bchelf/microNES/src/common/apu_micrones.c

#include "apu_micrones.h"

#include <math.h>
#include <string.h>

enum {
    APU_FRAME_STEP_1 = 3729,
    APU_FRAME_STEP_2 = 7457,
    APU_FRAME_STEP_3 = 11186,
    APU_FRAME_STEP_4 = 14915,
    APU_FRAME_STEP_5 = 18641,
};

static const uint8_t k_apu_length_table[32] = {
    10, 254, 20,  2, 40,  4, 80,  6,
    160, 8, 60, 10, 14, 12, 26, 14,
    12, 16, 24, 18, 48, 20, 96, 22,
    192, 24, 72, 26, 16, 28, 32, 30,
};

static const uint8_t k_apu_pulse_duty[4][8] = {
    { 0, 1, 0, 0, 0, 0, 0, 0 },
    { 0, 1, 1, 0, 0, 0, 0, 0 },
    { 0, 1, 1, 1, 1, 0, 0, 0 },
    { 1, 0, 0, 1, 1, 1, 1, 1 },
};

static const uint8_t k_apu_triangle_sequence[32] = {
    15, 14, 13, 12, 11, 10, 9, 8,
    7,  6,  5,  4,  3,  2,  1, 0,
    0,  1,  2,  3,  4,  5,  6, 7,
    8,  9, 10, 11, 12, 13, 14, 15,
};

static const uint16_t k_apu_noise_period_table[16] = {
    4, 8, 16, 32, 64, 96, 128, 160,
    202, 254, 380, 508, 762, 1016, 2034, 4068,
};

/* NTSC DMC rate table: CPU cycles per output-unit clock.
 * Source: NesDev wiki, APU DMC. PAL uses a different table; we are NTSC-only. */
static const uint16_t k_apu_dmc_rate_table[16] = {
    428, 380, 340, 320, 286, 254, 226, 214,
    190, 160, 142, 128, 106,  84,  72,  54,
};

enum {
    APU_TEST_TONE_PULSE_PHASE = 0,
    APU_TEST_TONE_TRIANGLE_PHASE = 1,
};

static const uint32_t k_apu_test_tone_step_pulse1 =
    (uint32_t)((440ull << 32) / APU_OUTPUT_SAMPLE_RATE);
static const uint32_t k_apu_test_tone_step_triangle =
    (uint32_t)((220ull << 32) / APU_OUTPUT_SAMPLE_RATE);

static void apu_stats_note(ApuDebugSampleStats *stats, int32_t value) {
#if MICRONES_ENABLE_APU_DEBUG_METRICS
    if (stats->sample_count == 0) {
        stats->min_value = value;
        stats->max_value = value;
    } else {
        if (value < stats->min_value) {
            stats->min_value = value;
        }
        if (value > stats->max_value) {
            stats->max_value = value;
        }
    }
    ++stats->sample_count;
    if (value != 0) {
        ++stats->nonzero_sample_count;
    }
    stats->abs_sum += (uint64_t)(value < 0 ? -value : value);
#else
    (void)stats;
    (void)value;
#endif
}

static void apu_pcm_push(Apu *apu, int16_t sample) {
    if (apu->pcm_count >= APU_PCM_CAPACITY) {
        ++apu->dropped_samples;
        return;
    }

    apu->pcm[apu->pcm_write_index] = sample;
    apu->pcm_write_index = (apu->pcm_write_index + 1u) % APU_PCM_CAPACITY;
    ++apu->pcm_count;
    ++apu->sample_count;
}

static void apu_capture_pulse_state(const ApuPulseChannel *src, ApuDebugPulseState *dst) {
    dst->enabled = src->enabled;
    dst->length_halt = src->length_halt;
    dst->constant_volume = src->constant_volume;
    dst->sweep_enabled = src->sweep_enabled;
    dst->duty = src->duty;
    dst->duty_step = src->duty_step;
    dst->volume_period = src->volume_period;
    dst->envelope_decay = src->envelope_decay;
    dst->length_counter = src->length_counter;
    dst->timer_period = src->timer_period;
    dst->timer_counter = src->timer_counter;
}

static void apu_capture_triangle_state(const ApuTriangleChannel *src, ApuDebugTriangleState *dst) {
    dst->enabled = src->enabled;
    dst->control_flag = src->control_flag;
    dst->linear_reload_flag = src->linear_reload_flag;
    dst->sequence_step = src->sequence_step;
    dst->linear_reload_value = src->linear_reload_value;
    dst->linear_counter = src->linear_counter;
    dst->length_counter = src->length_counter;
    dst->timer_period = src->timer_period;
    dst->timer_counter = src->timer_counter;
}

static void apu_capture_noise_state(const ApuNoiseChannel *src, ApuDebugNoiseState *dst) {
    dst->enabled = src->enabled;
    dst->length_halt = src->length_halt;
    dst->constant_volume = src->constant_volume;
    dst->mode = src->mode;
    dst->volume_period = src->volume_period;
    dst->envelope_decay = src->envelope_decay;
    dst->length_counter = src->length_counter;
    dst->period_index = src->period_index;
    dst->timer_period = src->timer_period;
    dst->timer_counter = src->timer_counter;
    dst->shift_register = src->shift_register;
}

static void apu_reset_debug_defaults(Apu *apu) {
    apu->mix_enable_mask = APU_DEBUG_MASK_ALL;
    apu->test_tone_mode = (uint8_t)APU_DEBUG_TEST_TONE_NONE;
    apu->test_tone_phase[APU_TEST_TONE_PULSE_PHASE] = 0;
    apu->test_tone_phase[APU_TEST_TONE_TRIANGLE_PHASE] = 0;
}

static uint16_t apu_pulse_sweep_target(const ApuPulseChannel *pulse) {
    uint16_t change = pulse->timer_period >> pulse->sweep_shift;
    if (pulse->sweep_negate) {
        return (uint16_t)(pulse->timer_period - change - (pulse->sweep_ones_complement ? 1u : 0u));
    }
    return (uint16_t)(pulse->timer_period + change);
}

static bool apu_pulse_sweep_muted(const ApuPulseChannel *pulse) {
    if (pulse->timer_period < 8u) {
        return true;
    }
    if (pulse->sweep_shift == 0u) {
        return false;
    }
    return apu_pulse_sweep_target(pulse) > 0x07ffu;
}

static uint8_t apu_pulse_volume(const ApuPulseChannel *pulse) {
    return pulse->constant_volume ? pulse->volume_period : pulse->envelope_decay;
}

static uint8_t apu_noise_volume(const ApuNoiseChannel *noise) {
    return noise->constant_volume ? noise->volume_period : noise->envelope_decay;
}

static void apu_clock_envelope(ApuPulseChannel *pulse) {
    if (pulse->envelope_start) {
        pulse->envelope_start = false;
        pulse->envelope_decay = 15;
        pulse->envelope_divider = pulse->volume_period;
        return;
    }

    if (pulse->envelope_divider > 0) {
        --pulse->envelope_divider;
        return;
    }

    pulse->envelope_divider = pulse->volume_period;
    if (pulse->envelope_decay > 0) {
        --pulse->envelope_decay;
    } else if (pulse->length_halt) {
        pulse->envelope_decay = 15;
    }
}

static void apu_clock_noise_envelope(ApuNoiseChannel *noise) {
    if (noise->envelope_start) {
        noise->envelope_start = false;
        noise->envelope_decay = 15;
        noise->envelope_divider = noise->volume_period;
        return;
    }

    if (noise->envelope_divider > 0) {
        --noise->envelope_divider;
        return;
    }

    noise->envelope_divider = noise->volume_period;
    if (noise->envelope_decay > 0) {
        --noise->envelope_decay;
    } else if (noise->length_halt) {
        noise->envelope_decay = 15;
    }
}

static void apu_clock_length(ApuPulseChannel *pulse) {
    if (!pulse->enabled) {
        pulse->length_counter = 0;
    } else if (!pulse->length_halt && pulse->length_counter > 0) {
        --pulse->length_counter;
    }
}

static void apu_clock_triangle_length(ApuTriangleChannel *triangle) {
    if (!triangle->enabled) {
        triangle->length_counter = 0;
    } else if (!triangle->control_flag && triangle->length_counter > 0) {
        --triangle->length_counter;
    }
}

static void apu_clock_noise_length(ApuNoiseChannel *noise) {
    if (!noise->enabled) {
        noise->length_counter = 0;
    } else if (!noise->length_halt && noise->length_counter > 0) {
        --noise->length_counter;
    }
}

static void apu_clock_triangle_linear(ApuTriangleChannel *triangle) {
    if (triangle->linear_reload_flag) {
        triangle->linear_counter = triangle->linear_reload_value;
    } else if (triangle->linear_counter > 0) {
        --triangle->linear_counter;
    }

    if (!triangle->control_flag) {
        triangle->linear_reload_flag = false;
    }
}

static void apu_clock_sweep(ApuPulseChannel *pulse) {
    bool do_update = (pulse->sweep_divider == 0) &&
                     pulse->sweep_enabled &&
                     pulse->sweep_shift > 0 &&
                     !apu_pulse_sweep_muted(pulse);

    if (do_update) {
        pulse->timer_period = apu_pulse_sweep_target(pulse);
    }

    if (pulse->sweep_divider == 0 || pulse->sweep_reload) {
        /* Spec: divider period is P+1 half-frames, so reload to P. */
        pulse->sweep_divider = pulse->sweep_period;
        pulse->sweep_reload = false;
    } else {
        --pulse->sweep_divider;
    }
}

static void apu_quarter_frame(Apu *apu) {
    apu_clock_envelope(&apu->pulse[0]);
    apu_clock_envelope(&apu->pulse[1]);
    apu_clock_noise_envelope(&apu->noise);
    apu_clock_triangle_linear(&apu->triangle);
}

static void apu_half_frame(Apu *apu) {
    apu_clock_length(&apu->pulse[0]);
    apu_clock_length(&apu->pulse[1]);
    apu_clock_triangle_length(&apu->triangle);
    apu_clock_noise_length(&apu->noise);
    apu_clock_sweep(&apu->pulse[0]);
    apu_clock_sweep(&apu->pulse[1]);
}

static void apu_clock_frame_counter(Apu *apu) {
    ++apu->frame_counter_cycle;

    if (!apu->frame_counter_mode_5) {
        switch (apu->frame_counter_cycle) {
        case APU_FRAME_STEP_1:
        case APU_FRAME_STEP_3:
            apu_quarter_frame(apu);
            break;
        case APU_FRAME_STEP_2:
            apu_quarter_frame(apu);
            apu_half_frame(apu);
            break;
        case APU_FRAME_STEP_4:
            apu_quarter_frame(apu);
            apu_half_frame(apu);
            apu->frame_counter_cycle = 0;
            ++apu->frame_counter_steps;
            break;
        default:
            break;
        }
        return;
    }

    switch (apu->frame_counter_cycle) {
    case APU_FRAME_STEP_1:
    case APU_FRAME_STEP_3:
        apu_quarter_frame(apu);
        break;
    case APU_FRAME_STEP_2:
        apu_quarter_frame(apu);
        apu_half_frame(apu);
        break;
    case APU_FRAME_STEP_5:
        apu_quarter_frame(apu);
        apu_half_frame(apu);
        apu->frame_counter_cycle = 0;
        ++apu->frame_counter_steps;
        break;
    default:
        break;
    }
}

/* The three per-cycle clock_*_timer functions below are kept only for unit
 * test reference. They are NOT called from the normal emulation path; timers
 * are advanced via the batched apu_timer_advance() calls in apu_step(). */
static void apu_clock_pulse_timer(ApuPulseChannel *pulse) {
    if (pulse->timer_counter == 0) {
        pulse->timer_counter = pulse->timer_period;
        pulse->duty_step = (uint8_t)((pulse->duty_step + 1u) & 0x07u);
    } else {
        --pulse->timer_counter;
    }
}

static void apu_clock_triangle_timer(ApuTriangleChannel *triangle) {
    if (triangle->timer_counter == 0) {
        triangle->timer_counter = triangle->timer_period;
        if (triangle->enabled &&
            triangle->length_counter > 0 &&
            triangle->linear_counter > 0 &&
            triangle->timer_period >= 2u) {
            triangle->sequence_step = (uint8_t)((triangle->sequence_step + 1u) & 0x1fu);
        }
    } else {
        --triangle->timer_counter;
    }
}

static void apu_clock_noise_timer(ApuNoiseChannel *noise) {
    uint16_t feedback;
    uint8_t tap_bit;

    if (noise->timer_counter == 0) {
        noise->timer_counter = noise->timer_period;
        tap_bit = noise->mode ? 6u : 1u;
        feedback = (uint16_t)((noise->shift_register & 0x0001u) ^
                              ((noise->shift_register >> tap_bit) & 0x0001u));
        noise->shift_register >>= 1;
        noise->shift_register |= (uint16_t)(feedback << 14);
    } else {
        --noise->timer_counter;
    }
}

static uint8_t apu_pulse_output(const ApuPulseChannel *pulse) {
    if (!pulse->enabled ||
        pulse->length_counter == 0 ||
        apu_pulse_sweep_muted(pulse) ||
        pulse->timer_period < 8u ||
        k_apu_pulse_duty[pulse->duty][pulse->duty_step] == 0) {
        return 0;
    }

    return apu_pulse_volume(pulse);
}

static uint8_t apu_triangle_output(const ApuTriangleChannel *triangle) {
    /* Real 2A03: when length/linear counters reach 0 the sequencer stops being
     * clocked but the DAC still emits the current sequence value. The NES's
     * analog HP filters then decay the held DC to 0 over ~30 ms. Returning 0
     * here produces an audible click at note-off; instead, rely on the HP in
     * apu_mix_sample to remove the held DC. The period<2 gate remains purely
     * to avoid aliasing through our nearest-sample mixer. */
    if (triangle->timer_period < 2u) {
        return 0;
    }
    return k_apu_triangle_sequence[triangle->sequence_step];
}

static uint8_t apu_noise_output(const ApuNoiseChannel *noise) {
    if (!noise->enabled ||
        noise->length_counter == 0 ||
        (noise->shift_register & 0x0001u) != 0) {
        return 0;
    }

    return apu_noise_volume(noise);
}

/* DMC memory reader: if the sample buffer is empty and there are bytes left
 * to fetch, read one byte from the CPU bus, wrap the address from $FFFF back
 * to $8000, and either halt on end-of-sample or loop per $4010 bit 6.
 * Real hardware stalls the CPU for 3-4 cycles on the fetch; we do not model
 * that here — it is inaudible for SMB1's short DMC samples. */
static void apu_dmc_memory_reader(Apu *apu) {
    ApuDmcChannel *d = &apu->dmc;
    if (d->sample_buffer_filled || d->bytes_remaining == 0u) {
        return;
    }
    if (apu->dmc_bus_read == NULL) {
        return;
    }
    d->sample_buffer = apu->dmc_bus_read(apu->dmc_bus_read_user, d->current_address);
    d->sample_buffer_filled = true;
    d->current_address = (uint16_t)(((d->current_address + 1u) & 0x7fffu) | 0x8000u);
    --d->bytes_remaining;
    if (d->bytes_remaining == 0u && d->loop_flag) {
        d->current_address = d->sample_address;
        d->bytes_remaining = d->sample_length;
    }
    /* IRQ on end-of-sample is intentionally not raised: SMB1 does not rely on
     * it, and there is no IRQ line wired from the APU in this engine. */
}

/* DMC output: clocked at the timer rate. If not silenced, the low bit of the
 * shift register steps output_level by ±2 (clamped to 0..127). When the shift
 * register is exhausted, reload from the sample buffer if available; else
 * latch silence. */
static void apu_dmc_output_clock(Apu *apu) {
    ApuDmcChannel *d = &apu->dmc;
    if (!d->silence_flag) {
        if ((d->shift_register & 0x01u) != 0u) {
            if (d->output_level <= 125u) d->output_level = (uint8_t)(d->output_level + 2u);
        } else {
            if (d->output_level >= 2u) d->output_level = (uint8_t)(d->output_level - 2u);
        }
    }
    d->shift_register >>= 1;
    if (d->bits_remaining > 0u) {
        --d->bits_remaining;
    }
    if (d->bits_remaining == 0u) {
        d->bits_remaining = 8u;
        if (d->sample_buffer_filled) {
            d->silence_flag = false;
            d->shift_register = d->sample_buffer;
            d->sample_buffer_filled = false;
            apu_dmc_memory_reader(apu);
        } else {
            d->silence_flag = true;
        }
    }
}

/* ---- NES hardware mixer lookup tables ----------------------------------------
 * The NES nonlinear mixing formula requires 6 float divides per sample:
 *   pulse_out = 95.88 / (8128/(p1+p2) + 100)        p1+p2 in 0..30
 *   tnd_out   = 159.79 / (1/(tri/8227 + n/12241) + 100)   tri,n in 0..15
 * At 800 samples/frame that's ~4800 float divides/frame. Precomputing these
 * as int16_t tables (built once at apu_init) reduces the hot path to two
 * table lookups + integer add. */
static int16_t s_pulse_mix_table[31];  /* index = pulse1+pulse2, 0..30   */
static int16_t s_tnd_mix_table[256];   /* index = triangle*16+noise, dmc=0 */
/* Scale: max combined NES output ≈ 0.6318; table values scaled so that sum
 * of both tables never exceeds INT16_MAX (tables individually may approach
 * ~13400 and ~19400 respectively). */
static const float k_mix_table_scale = 32767.0f / (0.258498f + 0.373355f);

static void apu_build_mix_tables(void) {
    int ps, tri, noise;
    for (ps = 1; ps <= 30; ++ps) {
        float v = 95.88f / (8128.0f / (float)ps + 100.0f);
        s_pulse_mix_table[ps] = (int16_t)lrintf(v * k_mix_table_scale);
    }
    s_pulse_mix_table[0] = 0;
    for (tri = 0; tri <= 15; ++tri) {
        for (noise = 0; noise <= 15; ++noise) {
            float tnd = (float)tri / 8227.0f + (float)noise / 12241.0f;
            float v = (tnd > 0.0f) ? 159.79f / (1.0f / tnd + 100.0f) : 0.0f;
            s_tnd_mix_table[tri * 16 + noise] = (int16_t)lrintf(v * k_mix_table_scale);
        }
    }
}

static int16_t MICRONES_HOT_FUNC(apu_mix_sample)(Apu *apu) {
    int32_t pulse1_raw = (int32_t)apu_pulse_output(&apu->pulse[0]);
    int32_t pulse2_raw = (int32_t)apu_pulse_output(&apu->pulse[1]);
    int32_t triangle_raw = (int32_t)apu_triangle_output(&apu->triangle);
    int32_t noise_raw = (int32_t)apu_noise_output(&apu->noise);
    int32_t dmc_raw = (int32_t)apu->dmc.output_level;  /* 0..127, held value */

    if (apu->test_tone_mode == APU_DEBUG_TEST_TONE_PULSE1) {
        apu->test_tone_phase[APU_TEST_TONE_PULSE_PHASE] += k_apu_test_tone_step_pulse1;
        pulse1_raw = (apu->test_tone_phase[APU_TEST_TONE_PULSE_PHASE] & 0x80000000u) ? 12 : 0;
        pulse2_raw = 0;
        triangle_raw = 0;
        noise_raw = 0;
        dmc_raw = 0;
    } else if (apu->test_tone_mode == APU_DEBUG_TEST_TONE_TRIANGLE) {
        uint32_t phase = apu->test_tone_phase[APU_TEST_TONE_TRIANGLE_PHASE] + k_apu_test_tone_step_triangle;
        apu->test_tone_phase[APU_TEST_TONE_TRIANGLE_PHASE] = phase;
        uint32_t step = phase >> 27;
        triangle_raw = (step < 16u) ? (int32_t)step : (int32_t)(31u - step);
        pulse1_raw = 0;
        pulse2_raw = 0;
        noise_raw = 0;
        dmc_raw = 0;
    }

    apu_stats_note(&apu->channel_stats[APU_DEBUG_CHANNEL_PULSE1], pulse1_raw);
    apu_stats_note(&apu->channel_stats[APU_DEBUG_CHANNEL_PULSE2], pulse2_raw);
    apu_stats_note(&apu->channel_stats[APU_DEBUG_CHANNEL_TRIANGLE], triangle_raw);
    apu_stats_note(&apu->channel_stats[APU_DEBUG_CHANNEL_NOISE], noise_raw);
    apu_stats_note(&apu->channel_stats[APU_DEBUG_CHANNEL_DMC], dmc_raw);

    /* Apply per-channel debug mute mask (all-on by default; no-op in production) */
    if (!(apu->mix_enable_mask & APU_DEBUG_MASK_PULSE1))   pulse1_raw = 0;
    if (!(apu->mix_enable_mask & APU_DEBUG_MASK_PULSE2))   pulse2_raw = 0;
    if (!(apu->mix_enable_mask & APU_DEBUG_MASK_TRIANGLE)) triangle_raw = 0;
    if (!(apu->mix_enable_mask & APU_DEBUG_MASK_NOISE))    noise_raw = 0;
    if (!(apu->mix_enable_mask & APU_DEBUG_MASK_DMC))      dmc_raw = 0;

    /* Pulse side: table lookup.  TND side: fast path when DMC is silent (the
     * precomputed table covers tri*16+noise with dmc=0).  When DMC is active
     * fall back to the exact non-linear formula for that sample.  SMB1 plays
     * DMC only during percussive hits so the slow path runs maybe 30% of the
     * time during music and never during silent frames. */
    int32_t tnd_mix;
    if (dmc_raw == 0) {
        tnd_mix = s_tnd_mix_table[triangle_raw * 16 + noise_raw];
    } else {
        float tnd = (float)triangle_raw / 8227.0f
                  + (float)noise_raw    / 12241.0f
                  + (float)dmc_raw      / 22638.0f;
        float v = 159.79f / (1.0f / tnd + 100.0f);
        tnd_mix = (int32_t)lrintf(v * k_mix_table_scale);
    }
    int32_t mixed_raw = (int32_t)s_pulse_mix_table[pulse1_raw + pulse2_raw] + tnd_mix;

    /* Stage 1 — first-order HP: y[n] = x[n] - x[n-1] + alpha * y[n-1].
     * alpha ≈ 0.988 → ~90 Hz corner @ 48 kHz, approximating the real 2A03's
     * combined ~90 Hz + ~440 Hz output HP stages.  Removes held DC (triangle
     * tail on note-off, mixer DC bias) and tightens note-on transients. */
    const float k_hp_alpha = 0.988f;
    float x = (float)mixed_raw;
    float y_hp = x - apu->hp_prev_x + k_hp_alpha * apu->hp_prev_y;
    apu->hp_prev_x = x;
    apu->hp_prev_y = y_hp;

    /* Stage 2 — first-order LP: y[n] = y[n-1] + alpha*(x[n] - y[n-1]).
     * alpha ≈ 0.84 → ~14 kHz corner @ 48 kHz.  Masks aliasing produced by
     * the mixer's nearest-sample snapshot of a 1.789 MHz APU (pulse duty
     * edges and high-pitch triangle steps fall above Nyquist). */
    const float k_lp_alpha = 0.84f;
    float y_lp = apu->lp_prev_y + k_lp_alpha * (y_hp - apu->lp_prev_y);
    apu->lp_prev_y = y_lp;

    int sample = (int)lrintf(y_lp);
    if (sample < -32768) {
        sample = -32768;
        ++apu->clip_count;
    } else if (sample > 32767) {
        sample = 32767;
        ++apu->clip_count;
    }
    apu_stats_note(&apu->channel_stats[APU_DEBUG_CHANNEL_FINAL_MIX], sample);
    return (int16_t)sample;
}

/* Advance a channel timer by n_cycles. Returns the number of times it fired.
 * Timers count down from period to 0, fire, then reset to period.
 * Period length in cycles = timer_period + 1.
 *
 * Marked inline (not MICRONES_HOT_FUNC) so the compiler expands it directly
 * into apu_step's inner loop, which is already in IRAM.  Eliminates ~3200
 * CALL8/ENTRY/RETW round-trips per frame (~73 µs at 240 MHz on LX7). */
static inline uint32_t apu_timer_advance(uint16_t *counter,
                                         uint16_t  period,
                                         uint32_t  n_cycles) {
    if (*counter >= n_cycles) {
        *counter -= (uint16_t)n_cycles;
        return 0;
    }
    uint32_t remaining = n_cycles - (uint32_t)*counter - 1u;
    uint32_t period1   = (uint32_t)period + 1u;
    uint32_t fires     = 1u + remaining / period1;
    *counter = (uint16_t)(period - remaining % period1);
    return fires;
}

void apu_init(Apu *apu) {
    apu_build_mix_tables();
    memset(apu, 0, sizeof(*apu));
    apu->pulse[0].sweep_ones_complement = true;
    apu->noise.shift_register = 1;
    /* Start the DMC timer at a valid rate so it clocks even before $4010 is
     * written.  Output remains 0 until $4011 or sample playback drives it. */
    apu->dmc.timer_period = k_apu_dmc_rate_table[0];
    apu->dmc.silence_flag = true;
    apu_reset_debug_defaults(apu);
}

void apu_reset(Apu *apu) {
    /* Preserve the HP/LP filter state across reset so the first post-reset
     * sample isn't a step from 0 to the mixer's DC bias (audible pop).  Also
     * preserve the DMC bus-read callback, which is wired once at Nes init. */
    float hp_prev_x = apu->hp_prev_x;
    float hp_prev_y = apu->hp_prev_y;
    float lp_prev_y = apu->lp_prev_y;
    ApuBusReadFn dmc_bus_read = apu->dmc_bus_read;
    void *dmc_bus_read_user = apu->dmc_bus_read_user;
    memset(apu, 0, sizeof(*apu));
    apu->hp_prev_x = hp_prev_x;
    apu->hp_prev_y = hp_prev_y;
    apu->lp_prev_y = lp_prev_y;
    apu->dmc_bus_read = dmc_bus_read;
    apu->dmc_bus_read_user = dmc_bus_read_user;
    apu->pulse[0].sweep_ones_complement = true;
    apu->noise.shift_register = 1;
    apu->dmc.timer_period = k_apu_dmc_rate_table[0];
    apu->dmc.silence_flag = true;
    apu_reset_debug_defaults(apu);
}

void apu_set_dmc_bus_read(Apu *apu, ApuBusReadFn fn, void *user) {
    apu->dmc_bus_read = fn;
    apu->dmc_bus_read_user = user;
}

#if MICRONES_ENABLE_APU_EMULATION
void MICRONES_HOT_FUNC(apu_step)(Apu *apu, uint32_t cpu_cycles) {
    if (cpu_cycles == 0) return;

    uint32_t cycles_left = cpu_cycles;

    do {
#if MICRONES_ENABLE_APU_PCM_OUTPUT
        /* Advance only to the next sample output point so each sample is mixed
         * from channel state that reflects timers up to that exact cycle.
         * cycles_to_next = ceil((APU_CPU_CLOCK_HZ - sample_phase) / RATE) */
        uint32_t to_next = (APU_CPU_CLOCK_HZ - apu->sample_phase + APU_OUTPUT_SAMPLE_RATE - 1u)
                           / APU_OUTPUT_SAMPLE_RATE;
        uint32_t cycles_this = to_next < cycles_left ? to_next : cycles_left;
#else
        uint32_t cycles_this = cycles_left;
#endif

        /* Compute APU-rate cycles (half CPU rate) for this sub-batch.
         * apu_cycles = number of even values in (old, old+cycles_this]. */
        uint32_t old_cpu = apu->cpu_cycles;
        apu->cpu_cycles += cycles_this;
        uint32_t apu_cycles = (old_cpu + cycles_this) / 2u - old_cpu / 2u;

        if (apu_cycles > 0) {
            /* --- Frame counter: clocked at APU rate --- */
            /* Processed before the triangle timer so that any length/linear counter
             * updates take effect before the sequencer is advanced this sub-batch. */
            {
                uint32_t old_fc = apu->frame_counter_cycle;
                uint32_t new_fc = old_fc + apu_cycles;
                /* Sub-batches are ≤38 CPU cycles (~19 APU cycles); thresholds are
                 * 3728+ apart, so at most one threshold crossing per sub-batch.
                 * Check from high to low so the reset case is handled first. */
                if (!apu->frame_counter_mode_5) {
                    if (old_fc < APU_FRAME_STEP_4 && new_fc >= APU_FRAME_STEP_4) {
                        apu_quarter_frame(apu); apu_half_frame(apu);
                        ++apu->frame_counter_steps;
                        new_fc = 0;
                    } else if (old_fc < APU_FRAME_STEP_3 && new_fc >= APU_FRAME_STEP_3) {
                        apu_quarter_frame(apu);
                    } else if (old_fc < APU_FRAME_STEP_2 && new_fc >= APU_FRAME_STEP_2) {
                        apu_quarter_frame(apu); apu_half_frame(apu);
                    } else if (old_fc < APU_FRAME_STEP_1 && new_fc >= APU_FRAME_STEP_1) {
                        apu_quarter_frame(apu);
                    }
                } else {
                    if (old_fc < APU_FRAME_STEP_5 && new_fc >= APU_FRAME_STEP_5) {
                        apu_quarter_frame(apu); apu_half_frame(apu);
                        ++apu->frame_counter_steps;
                        new_fc = 0;
                    } else if (old_fc < APU_FRAME_STEP_3 && new_fc >= APU_FRAME_STEP_3) {
                        apu_quarter_frame(apu);
                    } else if (old_fc < APU_FRAME_STEP_2 && new_fc >= APU_FRAME_STEP_2) {
                        apu_quarter_frame(apu); apu_half_frame(apu);
                    } else if (old_fc < APU_FRAME_STEP_1 && new_fc >= APU_FRAME_STEP_1) {
                        apu_quarter_frame(apu);
                    }
                }
                apu->frame_counter_cycle = new_fc;
            }

            /* --- Pulse timers: clocked at APU rate --- */
            {
                ApuPulseChannel *p = &apu->pulse[0];
                uint32_t fires = apu_timer_advance(&p->timer_counter, p->timer_period, apu_cycles);
                p->duty_step = (uint8_t)((p->duty_step + fires) & 0x07u);
            }
            {
                ApuPulseChannel *p = &apu->pulse[1];
                uint32_t fires = apu_timer_advance(&p->timer_counter, p->timer_period, apu_cycles);
                p->duty_step = (uint8_t)((p->duty_step + fires) & 0x07u);
            }

            /* --- Noise timer: clocked at APU rate --- */
            {
                ApuNoiseChannel *n = &apu->noise;
                uint32_t fires = apu_timer_advance(&n->timer_counter, n->timer_period, apu_cycles);
                uint8_t tap_bit = n->mode ? 6u : 1u;
                for (uint32_t i = 0; i < fires; ++i) {
                    uint16_t feedback = (uint16_t)((n->shift_register & 1u) ^
                                                   ((n->shift_register >> tap_bit) & 1u));
                    n->shift_register = (n->shift_register >> 1) | (uint16_t)(feedback << 14u);
                }
            }
        }

        /* --- Triangle timer: clocked every CPU cycle --- */
        /* Placed after the frame counter so length/linear counter changes from
         * this sub-batch's frame counter fire are visible before advancing the
         * sequencer. The output gate (timer_period < 2) is in apu_triangle_output,
         * not here; the timer itself runs unconditionally per NES hardware. */
        {
            ApuTriangleChannel *tri = &apu->triangle;
            uint32_t fires = apu_timer_advance(&tri->timer_counter, tri->timer_period, cycles_this);
            if (fires > 0 && tri->enabled && tri->length_counter > 0 &&
                    tri->linear_counter > 0) {
                tri->sequence_step = (uint8_t)((tri->sequence_step + fires) & 0x1fu);
            }
        }

        /* --- DMC timer: clocked every CPU cycle ---
         * Each fire advances the output unit one bit. The memory reader is
         * driven by the output unit (fetches on shift-register reload) so no
         * separate reader clock is needed. */
        {
            ApuDmcChannel *d = &apu->dmc;
            if (d->timer_period > 0u) {
                uint32_t fires = apu_timer_advance(&d->timer_counter, d->timer_period, cycles_this);
                for (uint32_t i = 0; i < fires; ++i) {
                    apu_dmc_output_clock(apu);
                }
            }
        }

#if MICRONES_ENABLE_APU_PCM_OUTPUT
        apu->sample_phase += APU_OUTPUT_SAMPLE_RATE * cycles_this;
        if (apu->sample_phase >= APU_CPU_CLOCK_HZ) {
            apu->sample_phase -= APU_CPU_CLOCK_HZ;
            apu_pcm_push(apu, apu_mix_sample(apu));
        }
#endif

        cycles_left -= cycles_this;
    } while (cycles_left > 0);
}
#endif

uint8_t apu_cpu_read(Apu *apu, uint16_t addr) {
    uint8_t status;

    if (addr != 0x4015u) {
        return 0;
    }

    status = 0;
    if (apu->pulse[0].length_counter > 0) {
        status |= 0x01u;
    }
    if (apu->pulse[1].length_counter > 0) {
        status |= 0x02u;
    }
    if (apu->triangle.length_counter > 0) {
        status |= 0x04u;
    }
    if (apu->noise.length_counter > 0) {
        status |= 0x08u;
    }
    if (apu->dmc.bytes_remaining > 0) {
        status |= 0x10u;
    }
    apu->status = status;
    return status;
}

void apu_cpu_write(Apu *apu, uint16_t addr, uint8_t value) {
    if (addr >= 0x4000u && addr <= 0x4017u) {
        apu->registers[addr - 0x4000u] = value;
        ++apu->register_write_count[addr - 0x4000u];
    }

    switch (addr) {
    case 0x4000u:
    case 0x4004u: {
        ApuPulseChannel *pulse = &apu->pulse[(addr - 0x4000u) / 4u];
        pulse->duty = (uint8_t)((value >> 6) & 0x03u);
        pulse->length_halt = (value & 0x20u) != 0;
        pulse->constant_volume = (value & 0x10u) != 0;
        pulse->volume_period = value & 0x0fu;
        break;
    }
    case 0x4001u:
    case 0x4005u: {
        ApuPulseChannel *pulse = &apu->pulse[(addr - 0x4001u) / 4u];
        pulse->sweep_enabled = (value & 0x80u) != 0;
        pulse->sweep_period = (uint8_t)((value >> 4) & 0x07u);
        pulse->sweep_negate = (value & 0x08u) != 0;
        pulse->sweep_shift = value & 0x07u;
        pulse->sweep_reload = true;
        break;
    }
    case 0x4002u:
    case 0x4006u: {
        ApuPulseChannel *pulse = &apu->pulse[(addr - 0x4002u) / 4u];
        pulse->timer_period = (uint16_t)((pulse->timer_period & 0x0700u) | value);
        /* Do not reset timer_counter here; only $4003/$4007 restarts the timer. */
        break;
    }
    case 0x4003u:
    case 0x4007u: {
        ApuPulseChannel *pulse = &apu->pulse[(addr - 0x4003u) / 4u];
        pulse->timer_period = (uint16_t)((pulse->timer_period & 0x00ffu) | ((uint16_t)(value & 0x07u) << 8));
        if (pulse->enabled) {
            pulse->length_counter = k_apu_length_table[(value >> 3) & 0x1fu];
        }
        /* Per NesDev APU_Pulse: writing the 4th register resets the sequencer
         * to position 0.  Without this, rapid note changes (e.g. the SMB1
         * end-of-level countdown trill on pulse 2) inherit a random duty
         * phase from the previous note; for duties 0/1/2, if the phase lands
         * inside a run of 0-bits the note plays silent for its entire brief
         * duration, collapsing the trill to a single audible pitch.  The
         * timer itself is free-running and reloads at its next expiry. */
        pulse->duty_step = 0;
        pulse->envelope_start = true;
        break;
    }
    case 0x4008u:
        apu->triangle.control_flag = (value & 0x80u) != 0;
        apu->triangle.linear_reload_value = value & 0x7fu;
        break;
    case 0x400au:
        apu->triangle.timer_period = (uint16_t)((apu->triangle.timer_period & 0x0700u) | value);
        /* Do not reset timer_counter: the triangle timer runs continuously. */
        break;
    case 0x400bu:
        apu->triangle.timer_period = (uint16_t)((apu->triangle.timer_period & 0x00ffu) | ((uint16_t)(value & 0x07u) << 8));
        if (apu->triangle.enabled) {
            apu->triangle.length_counter = k_apu_length_table[(value >> 3) & 0x1fu];
        }
         /* Clamp timer_counter to new period. Without this, a note change to a
         * shorter period leaves a stale large timer_counter. The first scanline
         * batch (n_cycles≈114) then causes apu_timer_advance to return a burst
         * of fires (e.g. fires=11) that skips sequence_step past positions 15/16
         * (value=0), producing an audible mid-wave click on every note change.
         * Clamping here matches real NES behavior where the timer never holds a
         * count larger than its current period. */
        if (apu->triangle.timer_counter > apu->triangle.timer_period) {
          apu->triangle.timer_counter = apu->triangle.timer_period;
        }
        apu->triangle.linear_reload_flag = true;
        break;
    case 0x400cu:
        apu->noise.length_halt = (value & 0x20u) != 0;
        apu->noise.constant_volume = (value & 0x10u) != 0;
        apu->noise.volume_period = value & 0x0fu;
        break;
    case 0x400eu:
        apu->noise.mode = (value & 0x80u) != 0;
        apu->noise.period_index = value & 0x0fu;
        apu->noise.timer_period = k_apu_noise_period_table[apu->noise.period_index];
        /* Do not reset timer_counter: the noise LFSR timer runs continuously. */
        break;
    case 0x400fu:
        if (apu->noise.enabled) {
            apu->noise.length_counter = k_apu_length_table[(value >> 3) & 0x1fu];
        }
        apu->noise.timer_counter = apu->noise.timer_period;
        apu->noise.envelope_start = true;
        break;
    case 0x4010u:
        apu->dmc.irq_enabled = (value & 0x80u) != 0;
        apu->dmc.loop_flag = (value & 0x40u) != 0;
        apu->dmc.rate_index = value & 0x0fu;
        apu->dmc.timer_period = k_apu_dmc_rate_table[apu->dmc.rate_index];
        break;
    case 0x4011u:
        /* Direct DAC load. Real 2A03 games (incl. SMB1 percussion) also use
         * $4011 to "bang" the DAC without DPCM playback; writing here updates
         * the output_level directly. Upper bit ignored per hardware. */
        apu->dmc.output_level = value & 0x7fu;
        break;
    case 0x4012u:
        /* Sample address: %11AAAAAA.AA000000 → $C000 + value*64 */
        apu->dmc.sample_address = (uint16_t)(0xc000u | ((uint16_t)value << 6));
        break;
    case 0x4013u:
        /* Sample length in bytes: %LLLL.LLLL0001 → value*16 + 1 */
        apu->dmc.sample_length = (uint16_t)(((uint16_t)value << 4) + 1u);
        break;
    case 0x4015u:
        apu->pulse[0].enabled = (value & 0x01u) != 0;
        apu->pulse[1].enabled = (value & 0x02u) != 0;
        apu->triangle.enabled = (value & 0x04u) != 0;
        apu->noise.enabled = (value & 0x08u) != 0;
        apu->dmc.enabled = (value & 0x10u) != 0;
        if (!apu->pulse[0].enabled) {
            apu->pulse[0].length_counter = 0;
        }
        if (!apu->pulse[1].enabled) {
            apu->pulse[1].length_counter = 0;
        }
        if (!apu->triangle.enabled) {
            apu->triangle.length_counter = 0;
            apu->triangle.linear_counter = 0;
        }
        if (!apu->noise.enabled) {
            apu->noise.length_counter = 0;
        }
        if (!apu->dmc.enabled) {
            apu->dmc.bytes_remaining = 0;
        } else if (apu->dmc.bytes_remaining == 0) {
            /* Restart playback: reset the memory reader pointer/length from
             * $4012/$4013 and immediately prefetch a byte so the output unit
             * has something to consume on the next reload. */
            apu->dmc.current_address = apu->dmc.sample_address;
            apu->dmc.bytes_remaining = apu->dmc.sample_length;
            apu_dmc_memory_reader(apu);
        }
        apu->status = value & 0x1fu;
        break;
    case 0x4017u:
        apu->frame_counter_mode_5 = (value & 0x80u) != 0;
        apu->frame_irq_inhibit = (value & 0x40u) != 0;
        apu->frame_counter_cycle = 0;
        if (apu->frame_counter_mode_5) {
            apu_quarter_frame(apu);
            apu_half_frame(apu);
        }
        break;
    default:
        break;
    }
}

uint32_t apu_output_sample_rate(const Apu *apu) {
    (void)apu;
    return APU_OUTPUT_SAMPLE_RATE;
}

size_t apu_audio_available_samples(const Apu *apu) {
    return apu->pcm_count;
}

size_t apu_audio_read_samples(Apu *apu, int16_t *dst, size_t max_samples) {
    size_t count = apu->pcm_count;

    if (count > max_samples) {
        count = max_samples;
    }

    for (size_t i = 0; i < count; ++i) {
        dst[i] = apu->pcm[apu->pcm_read_index];
        apu->pcm_read_index = (apu->pcm_read_index + 1u) % APU_PCM_CAPACITY;
    }
    apu->pcm_count -= (uint32_t)count;
    return count;
}

void apu_debug_set_mix_enable_mask(Apu *apu, uint8_t mask) {
    apu->mix_enable_mask = (uint8_t)(mask & APU_DEBUG_MASK_ALL);
}

uint8_t apu_debug_mix_enable_mask(const Apu *apu) {
    return apu->mix_enable_mask;
}

void apu_debug_set_test_tone(Apu *apu, ApuDebugTestTone mode) {
    apu->test_tone_mode = (uint8_t)mode;
    apu->test_tone_phase[APU_TEST_TONE_PULSE_PHASE] = 0;
    apu->test_tone_phase[APU_TEST_TONE_TRIANGLE_PHASE] = 0;
}

ApuDebugTestTone apu_debug_test_tone(const Apu *apu) {
    return (ApuDebugTestTone)apu->test_tone_mode;
}

void apu_debug_reset_metrics(Apu *apu) {
    memset(apu->channel_stats, 0, sizeof(apu->channel_stats));
    memset(apu->register_write_count, 0, sizeof(apu->register_write_count));
    apu->dropped_samples = 0;
    apu->clip_count = 0;
}

void apu_debug_get_report(const Apu *apu, ApuDebugReport *report) {
    memset(report, 0, sizeof(*report));
    report->mix_enable_mask = apu->mix_enable_mask;
    report->test_tone = (ApuDebugTestTone)apu->test_tone_mode;
    report->dropped_samples = apu->dropped_samples;
    report->clip_count = apu->clip_count;
    memcpy(report->channel_stats, apu->channel_stats, sizeof(report->channel_stats));
    for (size_t i = 0; i < APU_DEBUG_REGISTER_COUNT; ++i) {
        report->register_summary[i].write_count = apu->register_write_count[i];
        report->register_summary[i].last_value = apu->registers[i];
    }
    apu_capture_pulse_state(&apu->pulse[0], &report->pulse[0]);
    apu_capture_pulse_state(&apu->pulse[1], &report->pulse[1]);
    apu_capture_triangle_state(&apu->triangle, &report->triangle);
    apu_capture_noise_state(&apu->noise, &report->noise);
    report->status = apu->status;
    report->frame_counter_mode_5 = apu->frame_counter_mode_5;
    report->frame_irq_inhibit = apu->frame_irq_inhibit;
}

const char *apu_debug_channel_name(ApuDebugChannel channel) {
    switch (channel) {
    case APU_DEBUG_CHANNEL_PULSE1:
        return "pulse1";
    case APU_DEBUG_CHANNEL_PULSE2:
        return "pulse2";
    case APU_DEBUG_CHANNEL_TRIANGLE:
        return "triangle";
    case APU_DEBUG_CHANNEL_NOISE:
        return "noise";
    case APU_DEBUG_CHANNEL_DMC:
        return "dmc";
    case APU_DEBUG_CHANNEL_FINAL_MIX:
        return "mix";
    default:
        return "unknown";
    }
}

const char *apu_debug_test_tone_name(ApuDebugTestTone mode) {
    switch (mode) {
    case APU_DEBUG_TEST_TONE_PULSE1:
        return "pulse1";
    case APU_DEBUG_TEST_TONE_TRIANGLE:
        return "triangle";
    default:
        return "off";
    }
}
