bchelf/microNES/src/pico/audio_pwm.c

/*
 * audio_pwm.c  —  High-frequency PWM audio output (default GP16)
 *
 * Two PWM slices:
 *
 *   Carrier (GP from MICRONES_AUDIO_PIN, slice = pwm_gpio_to_slice_num):
 *     clkdiv = 1.0, wrap = 1023  →  315 MHz / 1024 ≈ 307.6 kHz
 *     Free-running, no interrupt.  10-bit resolution.
 *
 *   Sample-rate timer (slice 0, no GPIO):
 *     clkdiv = 1.25, wrap = 5249  →  315 MHz / (1.25 × 5250) = 48,000 Hz
 *     Wrap interrupt pops one sample and writes the carrier level.
 *
 * The ~307.6 kHz carrier is attenuated ~51 dB by the two-pole 15.9 kHz RC
 * filter, vs ~20 dB for the old 48 kHz carrier (which hummed).
 *
 * Sample conversion  int16 → PWM level (N = AUDIO_CARRIER_BITS = 10):
 *   level = ((int32_t)sample + 32768) >> (16 - N)
 *        maps [-32768..32767] → [0..1023] using the top N bits of every
 *        16-bit sample (mid-scale 512 = silence).
 */

#include "audio_pwm.h"
#include "clock_config.h"

#include "hardware/gpio.h"
#include "hardware/irq.h"
#include "hardware/pwm.h"

/* =========================================================================
 * PWM parameters
 * ========================================================================= */

enum {
    AUDIO_CARRIER_WRAP       = MICRONES_AUDIO_PWM_CARRIER_WRAP,  /* 1023 = 10-bit */
    AUDIO_CARRIER_BITS       = 10u,                  /* log2(AUDIO_CARRIER_WRAP + 1) */
    AUDIO_CARRIER_SHIFT      = 16u - AUDIO_CARRIER_BITS,  /* int16 → top N bits (=6) */
    AUDIO_LEVEL_SILENCE      = (AUDIO_CARRIER_WRAP + 1u) / 2u,  /* mid-scale (=512) */
    AUDIO_SAMPLE_TIMER_SLICE = 0u,   /* PWM slice 0: 48 kHz timer, no GPIO */
    AUDIO_BUF_SIZE           = 2048, /* ~42.7 ms at 48 kHz; power-of-2 for cheap modulo */
};

/* Keep the bit count in sync with the wrap define in clock_config.h. */
_Static_assert((1u << AUDIO_CARRIER_BITS) - 1u == AUDIO_CARRIER_WRAP,
               "AUDIO_CARRIER_BITS must match MICRONES_AUDIO_PWM_CARRIER_WRAP");

/* =========================================================================
 * Ring buffer (single-producer Core 0 / single-consumer Core 0 IRQ)
 * ========================================================================= */

static int16_t           audio_buf[AUDIO_BUF_SIZE];
static volatile uint32_t audio_buf_head  = 0;    /* consumer (IRQ) read position  */
static volatile uint32_t audio_buf_tail  = 0;    /* producer (main) write position */
static volatile uint32_t audio_underruns = 0;

static uint  s_audio_slice;
static uint16_t s_audio_last_level = AUDIO_LEVEL_SILENCE;  /* sample-and-hold across underruns */

/* =========================================================================
 * Sample-rate timer interrupt handler (Core 0)
 *
 * Fires at 48,000 Hz from timer slice 0.  Pops one sample from the ring
 * buffer and writes the level to the carrier slice on MICRONES_AUDIO_PIN.
 *
 * Execution time: ~10-15 instructions ≈ 10-15 sys_clk cycles.
 * At 315 MHz / 48,000 Hz = 6,562.5 cycles between interrupts, the ISR
 * consumes < 0.2% of Core 0's cycle budget.
 * ========================================================================= */

static void __isr pwm_audio_irq_handler(void) {
    pwm_clear_irq(AUDIO_SAMPLE_TIMER_SLICE);

    uint32_t head = audio_buf_head;
    uint32_t level;

    if (head == audio_buf_tail) {
        /* Underrun: hold last output level to suppress buzz */
        level = s_audio_last_level;
        ++audio_underruns;
    } else {
        /*
         * Convert int16 → unsigned PWM level using the top AUDIO_CARRIER_BITS.
         *   level = ((int32_t)sample + 32768) >> (16 - AUDIO_CARRIER_BITS)
         *   Maps: -32768 → 0,  0 → 512,  32767 → 1023
         */
        level = (uint32_t)((int32_t)audio_buf[head] + 32768) >> AUDIO_CARRIER_SHIFT;

        s_audio_last_level = (uint16_t)level;
        audio_buf_head = (head + 1u) & (AUDIO_BUF_SIZE - 1u);
    }

    pwm_set_gpio_level(MICRONES_AUDIO_PIN, level);
}

/* =========================================================================
 * audio_pwm_init()
 * ========================================================================= */

void audio_pwm_init(uint32_t sample_rate) {
    (void)sample_rate;   /* actual rate is fixed by clock_config.h for this target */

    /* --- Carrier PWM on MICRONES_AUDIO_PIN (free-running, ~1.23 MHz, 8-bit) - */
    gpio_set_function(MICRONES_AUDIO_PIN, GPIO_FUNC_PWM);
    s_audio_slice = pwm_gpio_to_slice_num(MICRONES_AUDIO_PIN);

    pwm_config carrier_cfg = pwm_get_default_config();
    pwm_config_set_clkdiv_int_frac(&carrier_cfg,
                                   MICRONES_AUDIO_PWM_CARRIER_CLKDIV_INT,
                                   MICRONES_AUDIO_PWM_CARRIER_CLKDIV_FRAC);
    pwm_config_set_wrap(&carrier_cfg, AUDIO_CARRIER_WRAP);
    pwm_init(s_audio_slice, &carrier_cfg, /*start=*/true);

    /* Initialise to mid-scale silence */
    pwm_set_gpio_level(MICRONES_AUDIO_PIN, AUDIO_LEVEL_SILENCE);

    audio_buf_head     = 0;
    audio_buf_tail     = 0;
    audio_underruns    = 0;
    s_audio_last_level = AUDIO_LEVEL_SILENCE;

    /* --- Sample-rate timer (slice 0, 48 kHz, interrupt-driven) ----------- */
    pwm_config timer_cfg = pwm_get_default_config();
    pwm_config_set_clkdiv_int_frac(&timer_cfg,
                                   MICRONES_AUDIO_PWM_CLKDIV_INT,
                                   MICRONES_AUDIO_PWM_CLKDIV_FRAC);
    pwm_config_set_wrap(&timer_cfg, MICRONES_AUDIO_PWM_WRAP);
    pwm_init(AUDIO_SAMPLE_TIMER_SLICE, &timer_cfg, /*start=*/true);

    /* Enable wrap interrupt on the timer slice only */
    pwm_clear_irq(AUDIO_SAMPLE_TIMER_SLICE);
    pwm_set_irq_enabled(AUDIO_SAMPLE_TIMER_SLICE, true);
    irq_set_exclusive_handler(PWM_IRQ_WRAP, pwm_audio_irq_handler);
    irq_set_enabled(PWM_IRQ_WRAP, true);
}

/* =========================================================================
 * audio_pwm_push_samples()
 * ========================================================================= */

size_t audio_pwm_push_samples(const int16_t *samples, size_t count) {
    size_t   written = 0;
    uint32_t tail    = audio_buf_tail;

    for (size_t i = 0; i < count; ++i) {
        uint32_t next_tail = (tail + 1u) & (AUDIO_BUF_SIZE - 1u);
        if (next_tail == audio_buf_head) {
            break;   /* buffer full — drop remainder silently */
        }
        audio_buf[tail] = samples[i];
        tail = next_tail;
        ++written;
    }

    audio_buf_tail = tail;
    return written;
}

/* =========================================================================
 * Diagnostics
 * ========================================================================= */

uint32_t audio_pwm_underrun_count(void) {
    return audio_underruns;
}

uint32_t audio_pwm_buffer_level(void) {
    uint32_t head = audio_buf_head;
    uint32_t tail = audio_buf_tail;
    return (tail - head) & (AUDIO_BUF_SIZE - 1u);
}
