bchelf/microNES/src/pico/rom_source_flash_cache.c

#include "rom_source_flash_cache.h"

#include "hardware/flash.h"
#include "hardware/regs/addressmap.h"
#include "hardware/sync.h"

#include "pico_video_backend.h"

#include <stdio.h>
#include <stdlib.h>
#include <stdarg.h>
#include <string.h>

#ifndef MICRONES_PICO_ENABLE_FLASH_ROM_CACHE
#define MICRONES_PICO_ENABLE_FLASH_ROM_CACHE 0
#endif

#ifndef MICRONES_PICO_FLASH_CACHE_OFFSET
#define MICRONES_PICO_FLASH_CACHE_OFFSET 0
#endif

#ifndef MICRONES_PICO_FLASH_CACHE_SIZE
#define MICRONES_PICO_FLASH_CACHE_SIZE 0
#endif

typedef struct {
    RomSource *backing;
} FlashCacheState;

typedef struct {
    uint32_t write_offset;
    uint8_t page[FLASH_PAGE_SIZE];
    size_t page_used;
    size_t bytes_programmed;
    size_t progress_base;
    size_t progress_total;
} FlashCacheWriter;

typedef struct {
    const uint8_t *xip;
    size_t offset;
    bool mismatch;
} FlashCacheCompare;

static FlashCacheState s_state;
static char s_last_error[160];
static FlashCacheProgressFn s_progress_fn;
static void *s_progress_user;

extern char __flash_binary_end;

static void set_error(const char *fmt, ...) {
    va_list ap;
    va_start(ap, fmt);
    vsnprintf(s_last_error, sizeof(s_last_error), fmt, ap);
    va_end(ap);
}

static uint32_t align_up_u32(uint32_t value, uint32_t align) {
    return (value + align - 1u) & ~(align - 1u);
}

static bool validate_cache_range(size_t rom_size, char *err, size_t err_size) {
    uintptr_t image_end = (uintptr_t)&__flash_binary_end - (uintptr_t)XIP_BASE;

    if (MICRONES_PICO_FLASH_CACHE_SIZE == 0u) {
        if (err && err_size) snprintf(err, err_size, "flash cache disabled");
        return false;
    }
    if ((uint32_t)image_end > (uint32_t)MICRONES_PICO_FLASH_CACHE_OFFSET) {
        if (err && err_size) {
            snprintf(err, err_size, "firmware overlaps flash cache (%u > %u)",
                     (unsigned)image_end,
                     (unsigned)MICRONES_PICO_FLASH_CACHE_OFFSET);
        }
        return false;
    }
    if (rom_size > (size_t)MICRONES_PICO_FLASH_CACHE_SIZE) {
        if (err && err_size) {
            snprintf(err, err_size, "ROM too large for flash cache (%u > %u)",
                     (unsigned)rom_size,
                     (unsigned)MICRONES_PICO_FLASH_CACHE_SIZE);
        }
        return false;
    }
    return true;
}

static void report_progress(size_t done, size_t total) {
    if (s_progress_fn != NULL) {
        s_progress_fn(done, total, s_progress_user);
    }
}

static bool flash_cache_program_page(FlashCacheWriter *writer) {
    uint32_t save = save_and_disable_interrupts();
    flash_range_program(writer->write_offset, writer->page, FLASH_PAGE_SIZE);
    restore_interrupts(save);
    writer->write_offset += FLASH_PAGE_SIZE;
    writer->bytes_programmed += FLASH_PAGE_SIZE;
    writer->page_used = 0;
    memset(writer->page, 0xff, sizeof(writer->page));

    size_t pages_done = writer->bytes_programmed / FLASH_PAGE_SIZE;
    report_progress(writer->progress_base + pages_done, writer->progress_total);

    return true;
}

static bool flash_cache_write(void *user, const uint8_t *data, size_t size) {
    FlashCacheWriter *writer = (FlashCacheWriter *)user;

    while (size > 0) {
        size_t space = FLASH_PAGE_SIZE - writer->page_used;
        size_t copy = size < space ? size : space;
        memcpy(&writer->page[writer->page_used], data, copy);
        writer->page_used += copy;
        data += copy;
        size -= copy;

        if (writer->page_used == FLASH_PAGE_SIZE) {
            flash_cache_program_page(writer);
        }
    }
    return true;
}

static bool flash_cache_flush(FlashCacheWriter *writer) {
    if (writer->page_used == 0) {
        return true;
    }
    return flash_cache_program_page(writer);
}

static bool flash_cache_compare_write(void *user, const uint8_t *data, size_t size) {
    FlashCacheCompare *cmp = (FlashCacheCompare *)user;

    if (memcmp(cmp->xip + cmp->offset, data, size) != 0) {
        cmp->mismatch = true;
        return false;
    }
    cmp->offset += size;
    return true;
}

static size_t cached_count(RomSource *self) {
    FlashCacheState *st = (FlashCacheState *)self->user;
    return (st->backing != NULL && st->backing->count != NULL)
        ? st->backing->count(st->backing)
        : 0u;
}

static const RomSourceEntry *cached_entry(RomSource *self, size_t index) {
    FlashCacheState *st = (FlashCacheState *)self->user;
    return (st->backing != NULL && st->backing->entry != NULL)
        ? st->backing->entry(st->backing, index)
        : NULL;
}
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
